ABillBlakely/Zinc-Box/LTSpice/Power supply.asc

C1: cap; 220µ
C2: cap; 220µ
C3: cap; 0.1µ
D1: diode; 1n4007
LOAD: current; 40m
R1: res; 10
V1: voltage; SINE(0 25 60)
X1: MC78XX; MC7815C
Named nets: 0
.tran 0 2.5 2
.MODEL 1n4007 d
+IS=7.02767e-09 RS=0.0341512 N=1.80803 EG=1.05743
+XTI=5 BV=1000 IBV=5e-08 CJO=1e-11
+VJ=0.7 M=0.5 FC=0.5 TT=1e-07
+KF=0 AF=1
.inc MC78XX.txt
25 volts peak is around 18 Vrms. 
Approx. what the "16VAC" wall wart 
supply measures under small load.
0.1uF is the minimum value for C3
It can be larger but increasing this 
has minimal effect.
40 mA is much higher than what we 
would expect, so good performance 
here should be better at our actual load.
This text sets up the models 
for the diode and regulator.
This is the simulation command, 
right click to adjust simulation.
