ABillBlakely/Zinc-Box/LTSpice/cartridge loading.asc

L1: ind; 100m
R2: res; 47k
R: res; 1200
V1: voltage; ""; AC 1
Named nets: 0
.ac oct 20 20 100k
