ABillBlakely/Zinc-Box/LTSpice/Signal path.asc

C1: cap; 150p
C2: cap; 2.2µ
C3: cap; .047µ
C4: cap; .01µ
C5: cap; 2.2µ
C6: cap; 3.3n
C7: cap; 150µ
I2: current; 200n
R1: res; 100k
R2: res; 100k
R3: res; 68k
R4: res; 6.8k
R5: res; 220
R6: res; 100k
R7: res; 500
U1: opamp
V1: voltage; SINE(0.3m 0 1k); AC 1
X1: RIAAIdeal
Named nets: 0, out, in, Ideal
.lib opamp.sub
.step param X list 3n 3.3n
.ac lin 8192 5.38 44100.0
R4 * C4 = 75 usec
C3 * R4 = 318 usec
R3 * C3 = 3180 uSec
