ABillBlakely/Zinc-Box/LTSpice/RIAAIdeal.asc

C1: cap; 1µ
C2: cap; 1µ
C3: cap; 1µ
R1: res; 3180
R2: res; 75
R3: res; 318
R4: res; 10k
R5: res; 10
U1: opamp
U2: opamp
U3: opamp
U4: opamp; Aol=1000K
Named nets: 0, RIAAOut, In
.lib opamp.sub
.ac dec 100 20 20k
